TheAbdullahSaleem/Mechanical-keyboard/assets/KEYCAPS/2u_r2.step

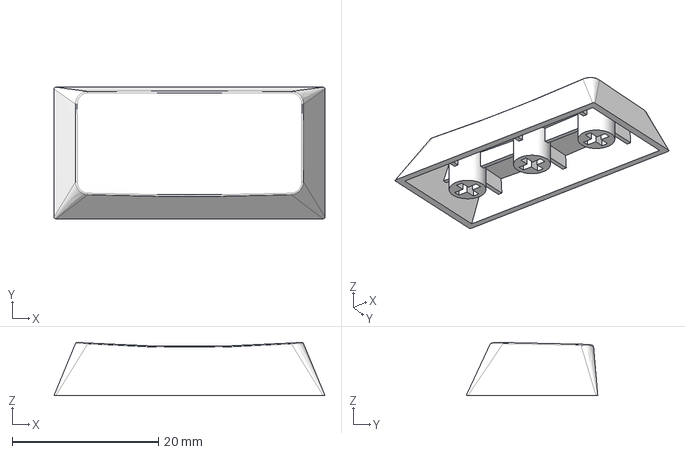
[picture p15: CAD file, 2026-10-03]
assets/KEYCAPS/2u_r2.step
37.1 x 18.0 x 7.25 mm
