TheAbdullahSaleem/Mechanical-keyboard/assets/KEYCAPS/Unnamed1-Product047Product033.step

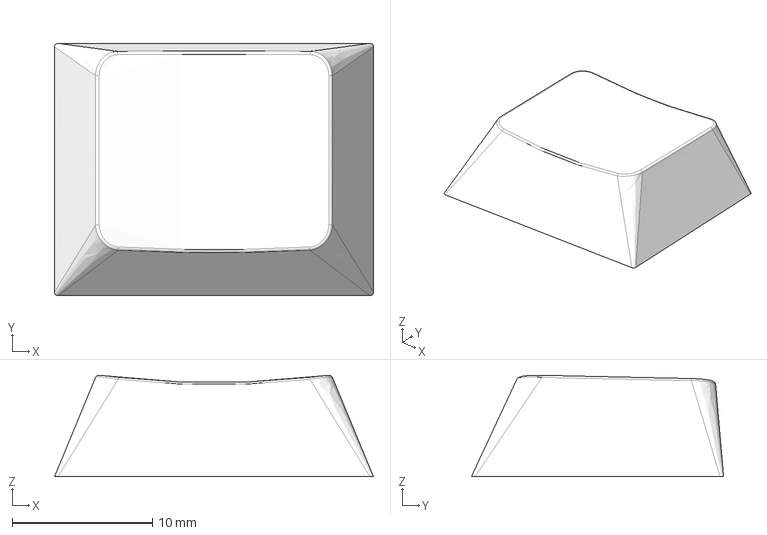
[picture p16: CAD file, 2026-10-03]
assets/KEYCAPS/Unnamed1-Product047Product033.step
22.8 x 18.0 x 7.24 mm
