TheAbdullahSaleem/Mechanical-keyboard/assets/KEYCAPS/1.5u_r1.step

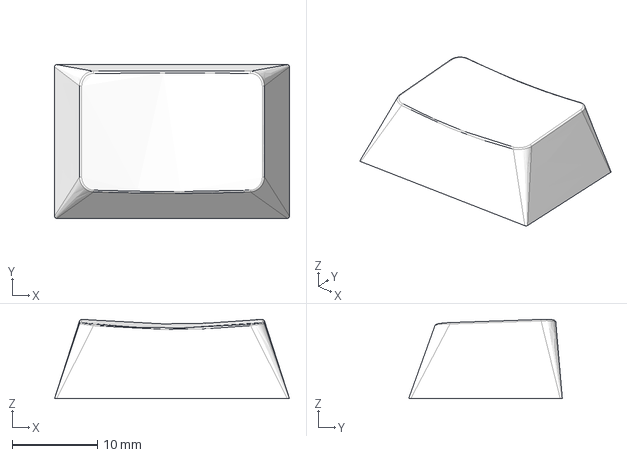
[picture p17: CAD file, 2026-10-03]
assets/KEYCAPS/1.5u_r1.step
27.5 x 18.0 x 9.28 mm
