TheAbdullahSaleem/Mechanical-keyboard/assets/KEYCAPS/2.75u_sb.step

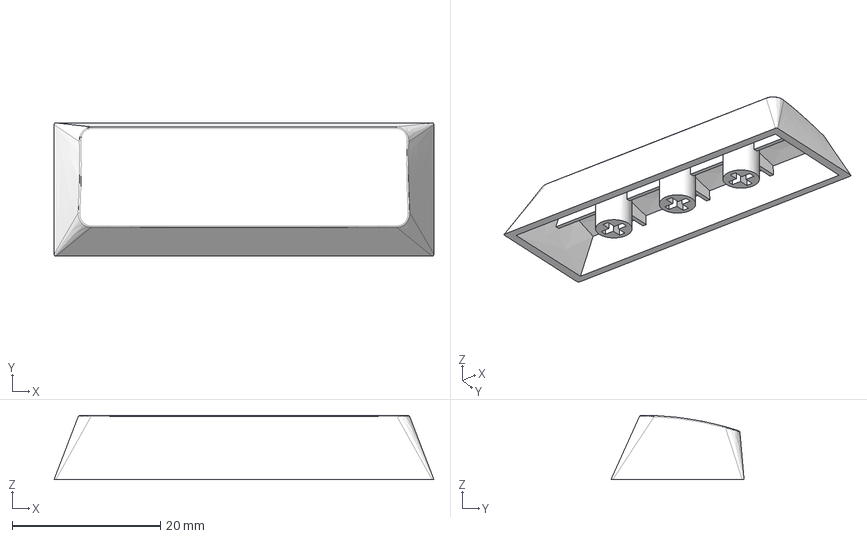
[picture p18: CAD file, 2026-10-03]
assets/KEYCAPS/2.75u_sb.step
51.3 x 18.0 x 8.70 mm
