TheAbdullahSaleem/Mechanical-keyboard/assets/KEYCAPS/2.25u_r4.step

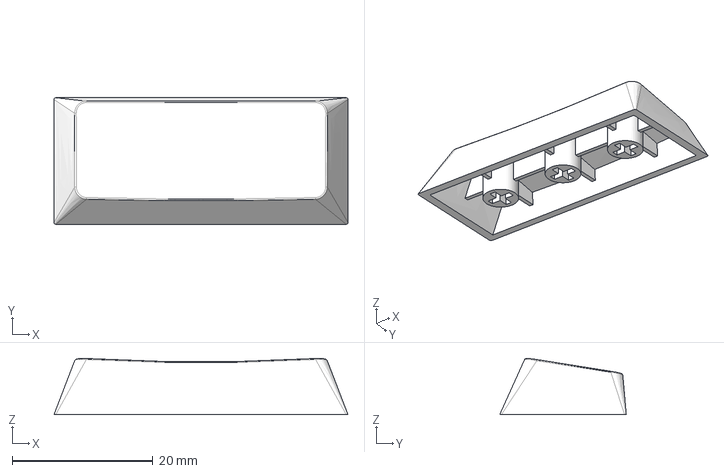
[picture p19: CAD file, 2026-10-03]
assets/KEYCAPS/2.25u_r4.step
41.8 x 18.0 x 7.99 mm
