TheAbdullahSaleem/Mechanical-keyboard/assets/KEYCAPS/1.25u_sb.step

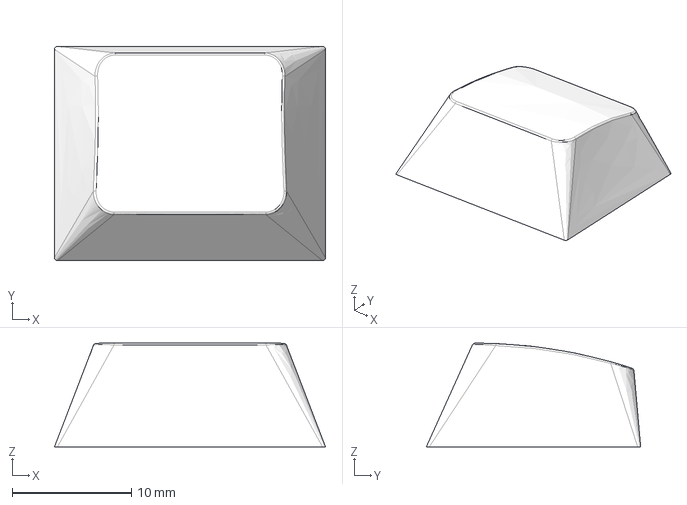
[picture p21: CAD file, 2026-10-03]
assets/KEYCAPS/1.25u_sb.step
22.8 x 18.0 x 8.70 mm
