TheAbdullahSaleem/Mechanical-keyboard/assets/KEYCAPS/1u_r3.step

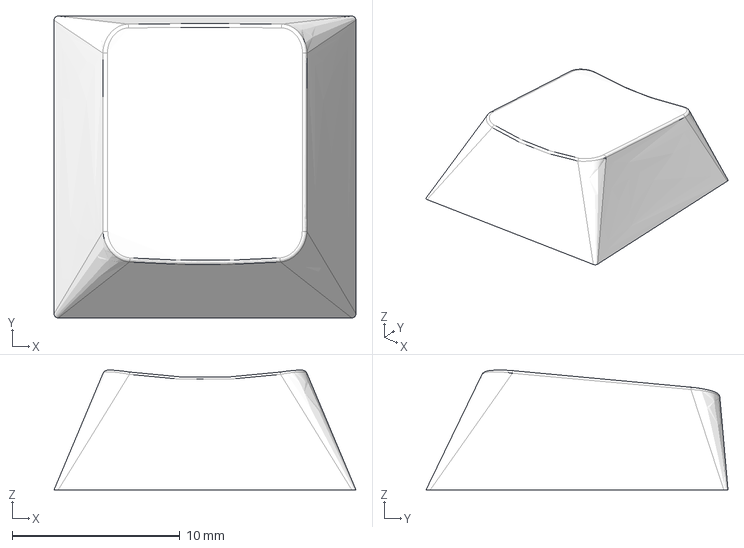
[picture p22: CAD file, 2026-10-03]
assets/KEYCAPS/1u_r3.step
18.0 x 18.0 x 7.15 mm
