TheAbdullahSaleem/Mechanical-keyboard/assets/KEYCAPS/1u_r4.step

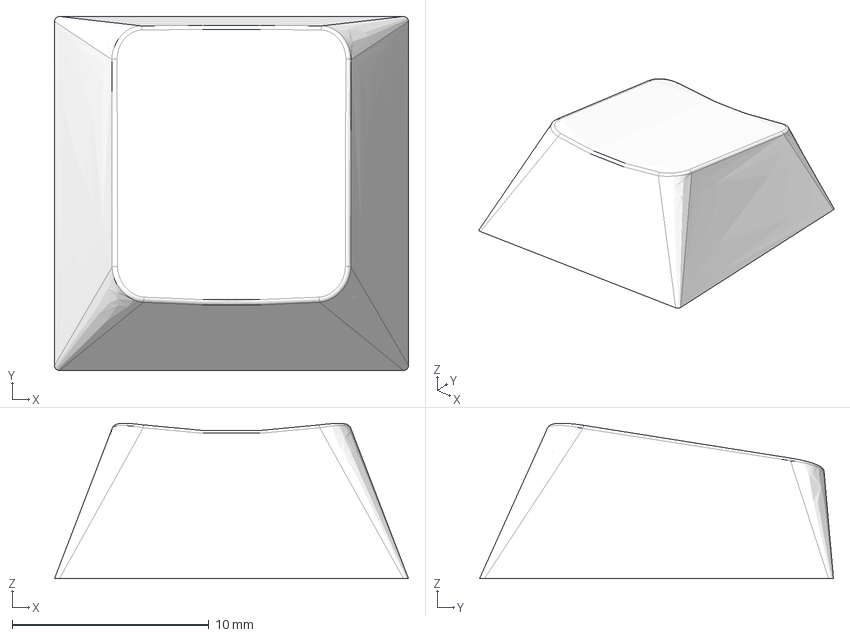
[picture p23: CAD file, 2026-10-03]
assets/KEYCAPS/1u_r4.step
18.0 x 18.0 x 7.90 mm
