TheAbdullahSaleem/Mechanical-keyboard/assets/KEYCAPS/2.5u_r2.step

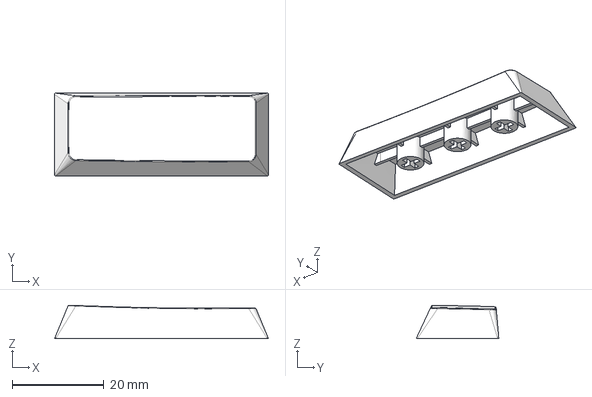
[picture p24: CAD file, 2026-10-03]
assets/KEYCAPS/2.5u_r2.step
46.6 x 18.0 x 7.26 mm
