TheAbdullahSaleem/Mechanical-keyboard/assets/KEYCAPS/1.75u_sb.step

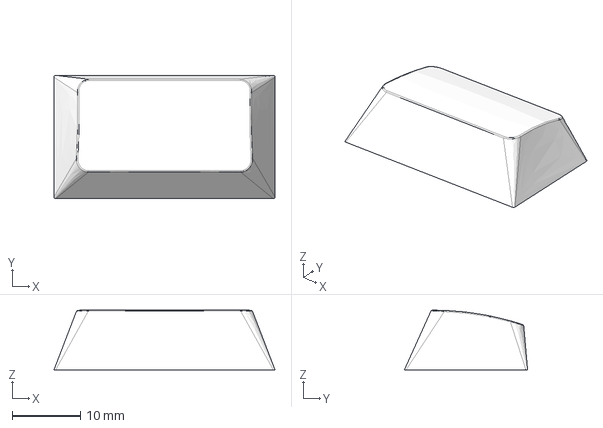
[picture p25: CAD file, 2026-10-03]
assets/KEYCAPS/1.75u_sb.step
32.3 x 18.0 x 8.70 mm
