TheAbdullahSaleem/Mechanical-keyboard/assets/KEYCAPS/2u_r4.step

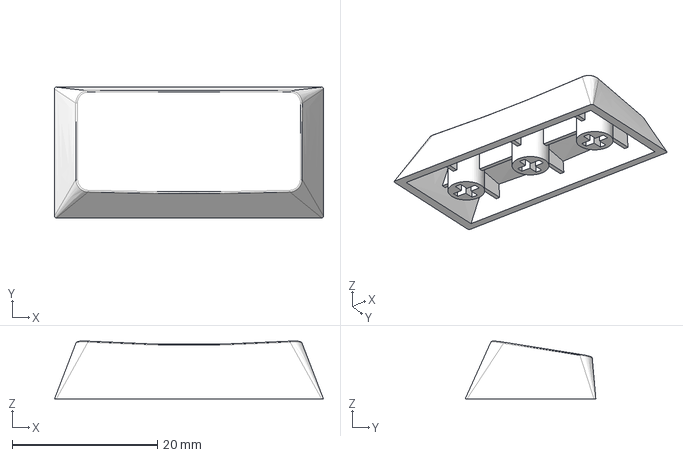
[picture p26: CAD file, 2026-10-03]
assets/KEYCAPS/2u_r4.step
37.1 x 18.0 x 7.98 mm
