TheAbdullahSaleem/Mechanical-keyboard/assets/KEYCAPS/2.5u_r3.step

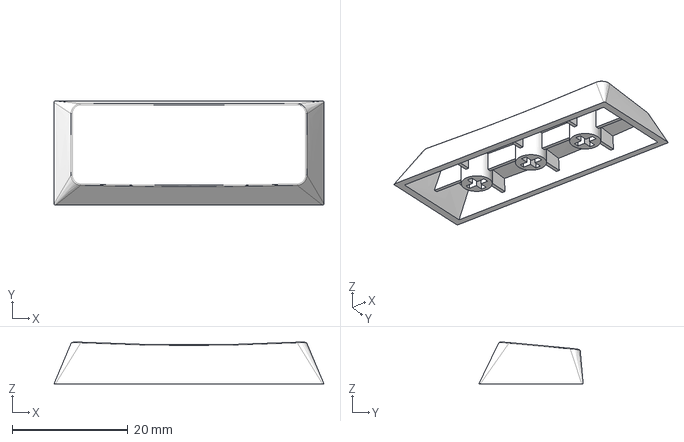
[picture p27: CAD file, 2026-10-03]
assets/KEYCAPS/2.5u_r3.step
46.6 x 18.0 x 7.21 mm
