TheAbdullahSaleem/Mechanical-keyboard/assets/KEYCAPS/2u_r1.step

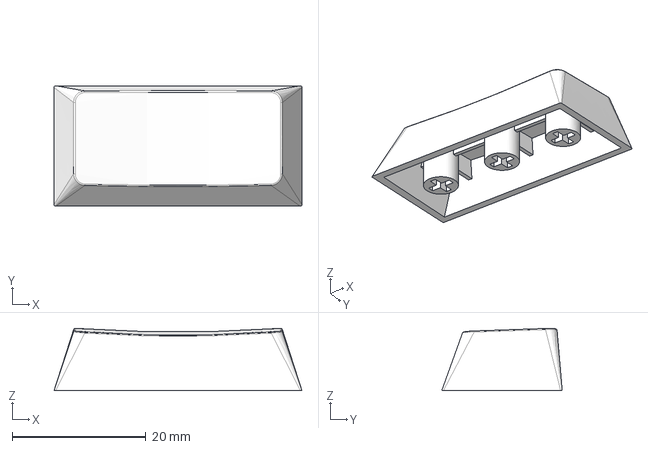
[picture p28: CAD file, 2026-10-03]
assets/KEYCAPS/2u_r1.step
37.1 x 18.0 x 9.29 mm
