TheAbdullahSaleem/Mechanical-keyboard/assets/KEYCAPS/1.25u_r4.step

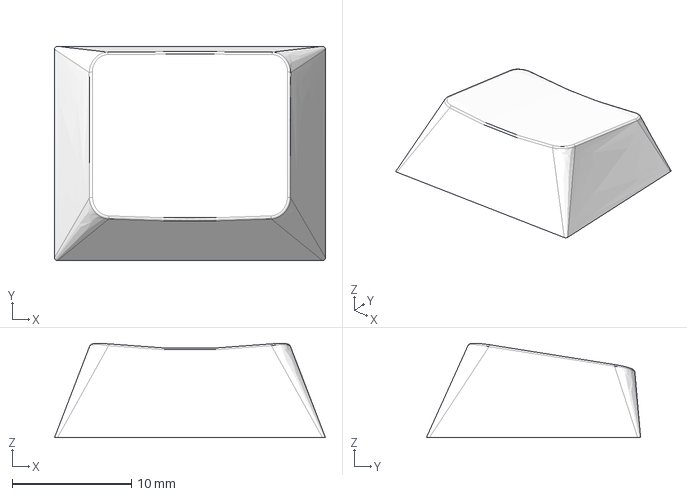
[picture p29: CAD file, 2026-10-03]
assets/KEYCAPS/1.25u_r4.step
22.8 x 18.0 x 7.93 mm
