TheAbdullahSaleem/Mechanical-keyboard/assets/KEYCAPS/2.75u_r1.step

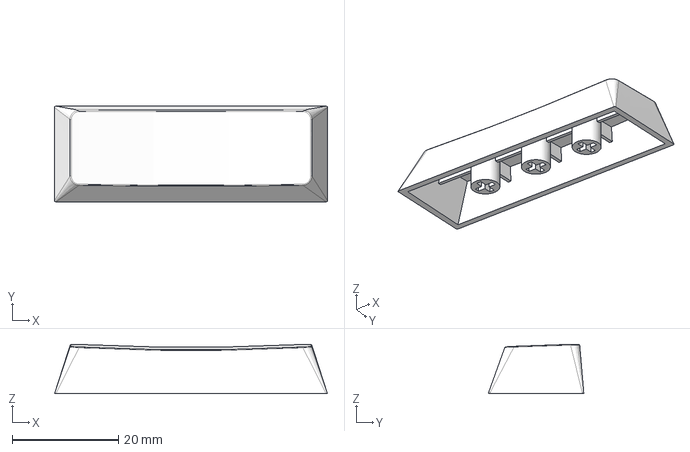
[picture p30: CAD file, 2026-10-03]
assets/KEYCAPS/2.75u_r1.step
51.3 x 18.0 x 9.30 mm
