TheAbdullahSaleem/Mechanical-keyboard/assets/KEYCAPS/1u_sb.step

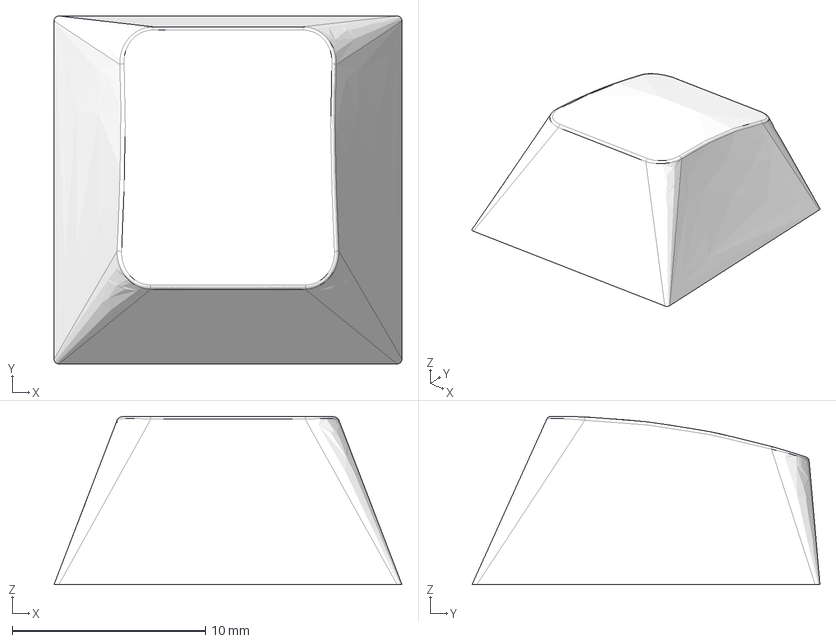
[picture p31: CAD file, 2026-10-03]
assets/KEYCAPS/1u_sb.step
18.0 x 18.0 x 8.70 mm
