TheAbdullahSaleem/Mechanical-keyboard/assets/KEYCAPS/6.25u_sb.step

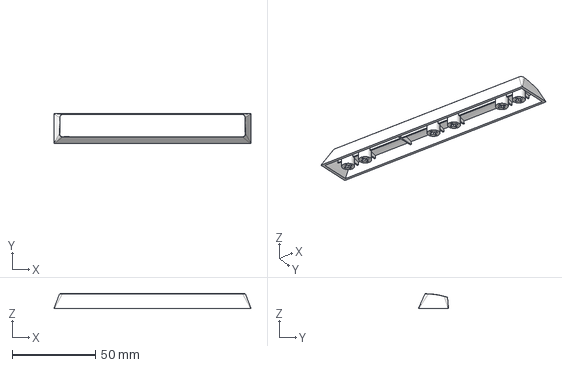
[picture p32: CAD file, 2026-10-03]
assets/KEYCAPS/6.25u_sb.step
118.0 x 18.0 x 8.70 mm
