TheAbdullahSaleem/Mechanical-keyboard/assets/KEYCAPS/2u_sb.step

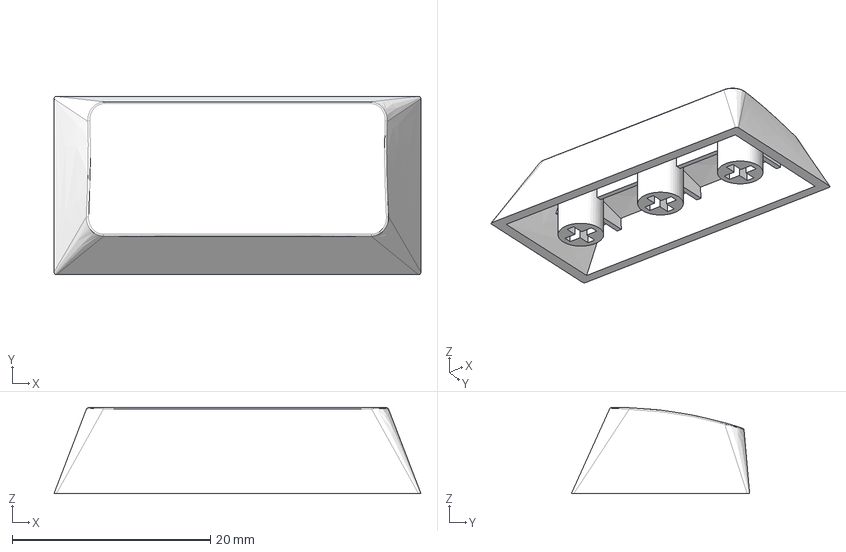
[picture p33: CAD file, 2026-10-03]
assets/KEYCAPS/2u_sb.step
37.1 x 18.0 x 8.70 mm
