TheAbdullahSaleem/Mechanical-keyboard/assets/KEYCAPS/1.75u_r1.step

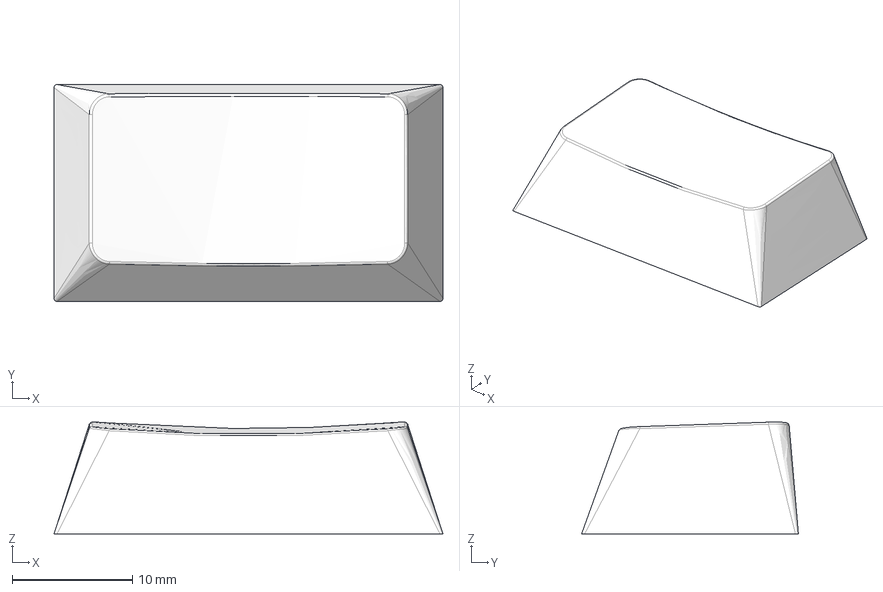
[picture p34: CAD file, 2026-10-03]
assets/KEYCAPS/1.75u_r1.step
32.3 x 18.0 x 9.29 mm
