TheAbdullahSaleem/Mechanical-keyboard/assets/KEYCAPS/1.5u_r4.step

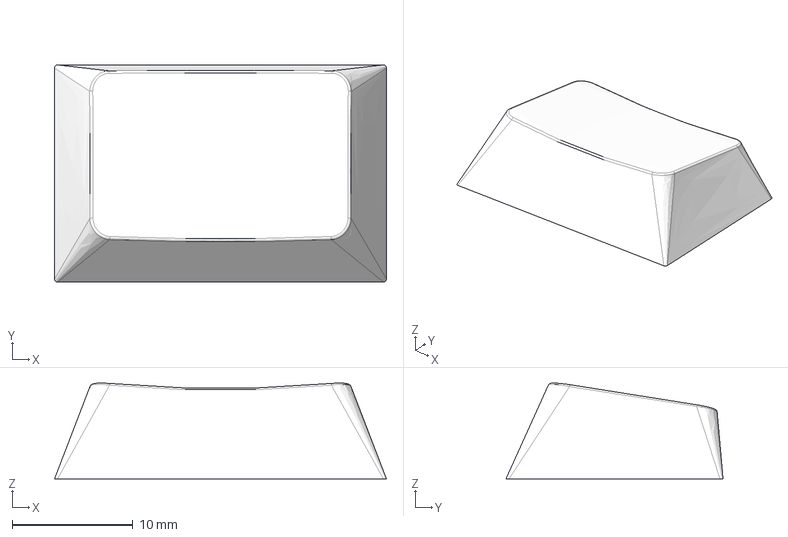
[picture p35: CAD file, 2026-10-03]
assets/KEYCAPS/1.5u_r4.step
27.5 x 18.0 x 7.95 mm
