TheAbdullahSaleem/Mechanical-keyboard/assets/KEYCAPS/2.5u_sb.step

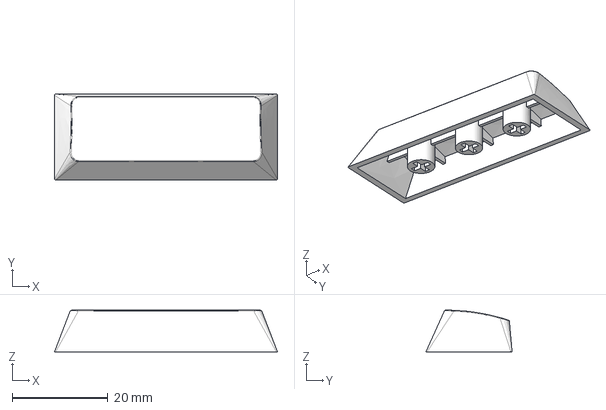
[picture p36: CAD file, 2026-10-03]
assets/KEYCAPS/2.5u_sb.step
46.6 x 18.0 x 8.70 mm
