TheAbdullahSaleem/Mechanical-keyboard/assets/KEYCAPS/1.25_r1.step

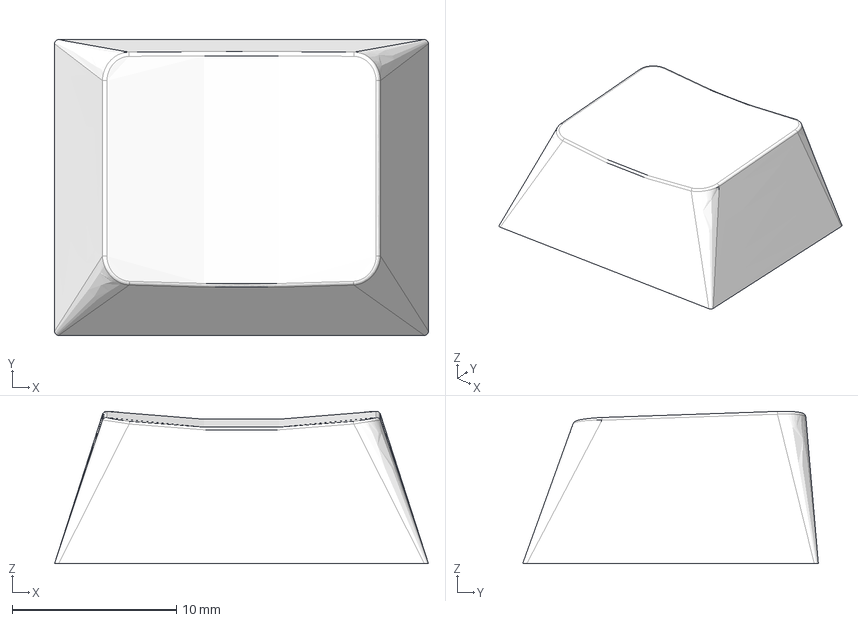
[picture p37: CAD file, 2026-10-03]
assets/KEYCAPS/1.25_r1.step
22.8 x 18.0 x 9.27 mm
