TheAbdullahSaleem/Mechanical-keyboard/assets/KEYCAPS/2.25u_r3.step

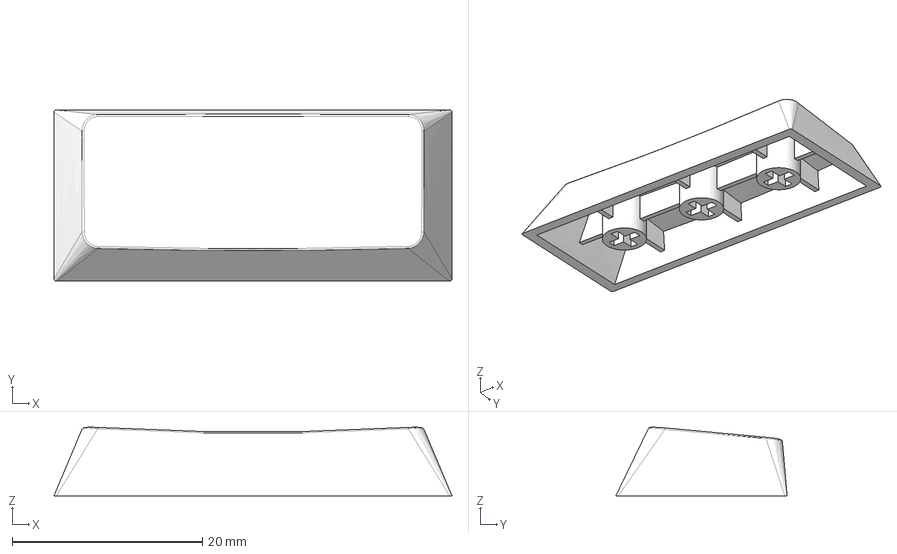
[picture p38: CAD file, 2026-10-03]
assets/KEYCAPS/2.25u_r3.step
41.8 x 18.0 x 7.21 mm
