TheAbdullahSaleem/Mechanical-keyboard/assets/KEYCAPS/2.5u_r1.step

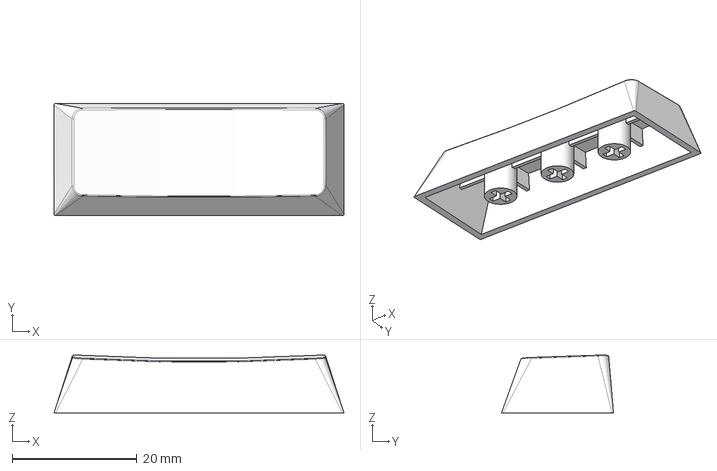
[picture p39: CAD file, 2026-10-03]
assets/KEYCAPS/2.5u_r1.step
46.6 x 18.0 x 9.30 mm
