TheAbdullahSaleem/Mechanical-keyboard/assets/KEYCAPS/2.75u_r3.step

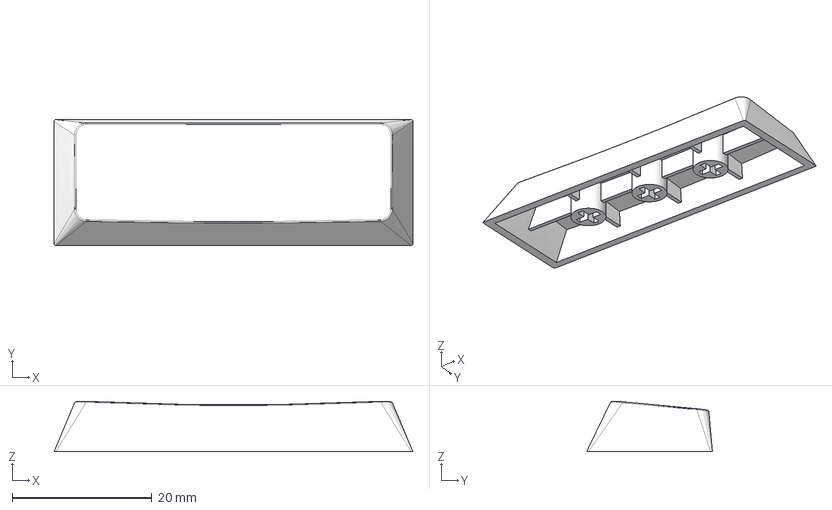
[picture p40: CAD file, 2026-10-03]
assets/KEYCAPS/2.75u_r3.step
51.3 x 18.0 x 7.22 mm
