TheAbdullahSaleem/Mechanical-keyboard/assets/KEYCAPS/2.25u_r1.step

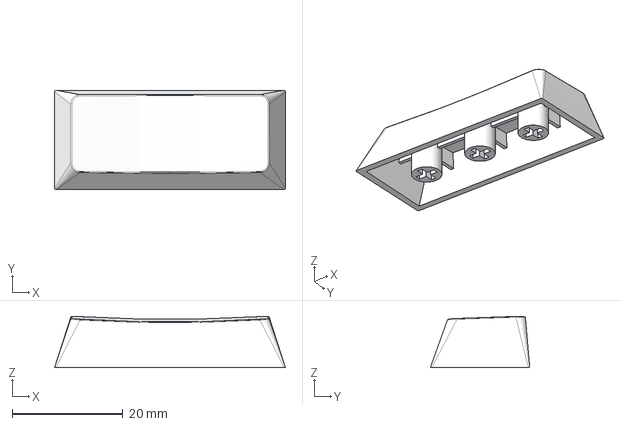
[picture p41: CAD file, 2026-10-03]
assets/KEYCAPS/2.25u_r1.step
41.8 x 18.0 x 9.30 mm
