TheAbdullahSaleem/Mechanical-keyboard/assets/KEYCAPS/2.25u_sb.step

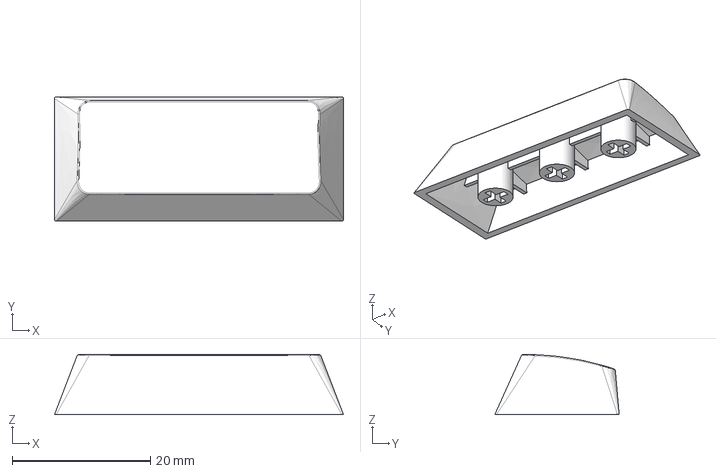
[picture p42: CAD file, 2026-10-03]
assets/KEYCAPS/2.25u_sb.step
41.8 x 18.0 x 8.70 mm
