TheAbdullahSaleem/Mechanical-keyboard/assets/KEYCAPS/1.5u_sb.step

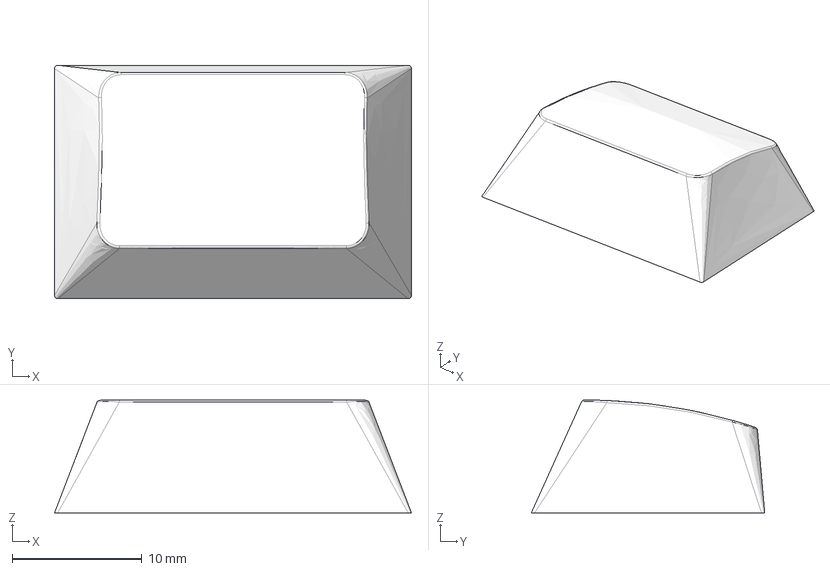
[picture p43: CAD file, 2026-10-03]
assets/KEYCAPS/1.5u_sb.step
27.5 x 18.0 x 8.70 mm
