TheAbdullahSaleem/Mechanical-keyboard/assets/KEYCAPS/2.5u_r4.step

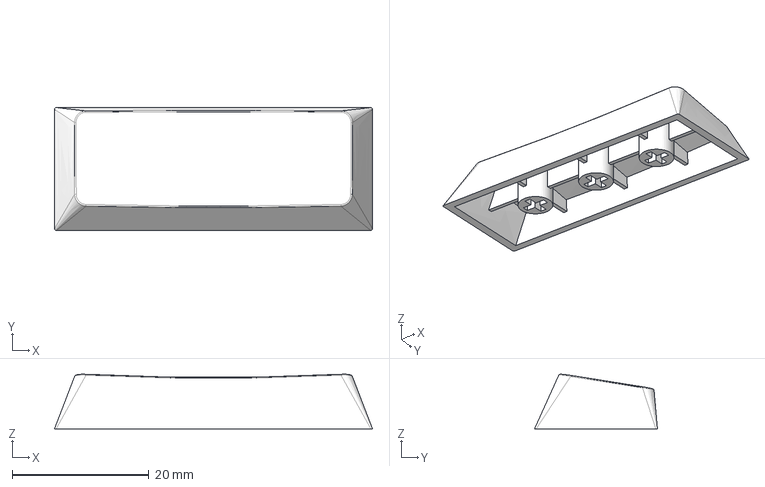
[picture p44: CAD file, 2026-10-03]
assets/KEYCAPS/2.5u_r4.step
46.6 x 18.0 x 8.00 mm
