TheAbdullahSaleem/Mechanical-keyboard/assets/KEYCAPS/1.75u_r3.step

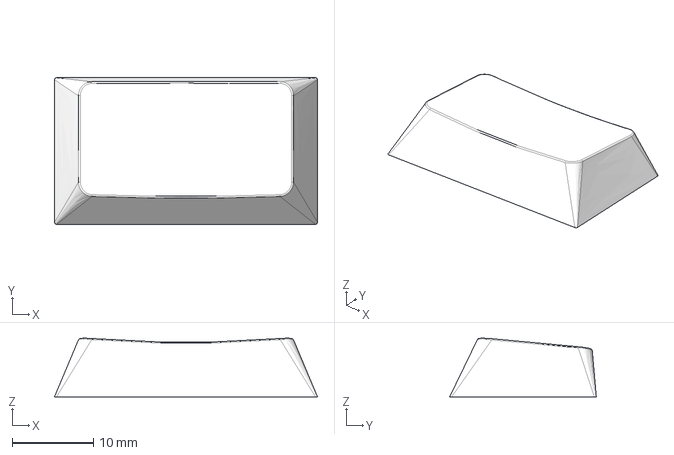
[picture p45: CAD file, 2026-10-03]
assets/KEYCAPS/1.75u_r3.step
32.3 x 18.0 x 7.19 mm
